Claptrap-Engineering/Mididuino/PCB Images/IMG_4418.JPG

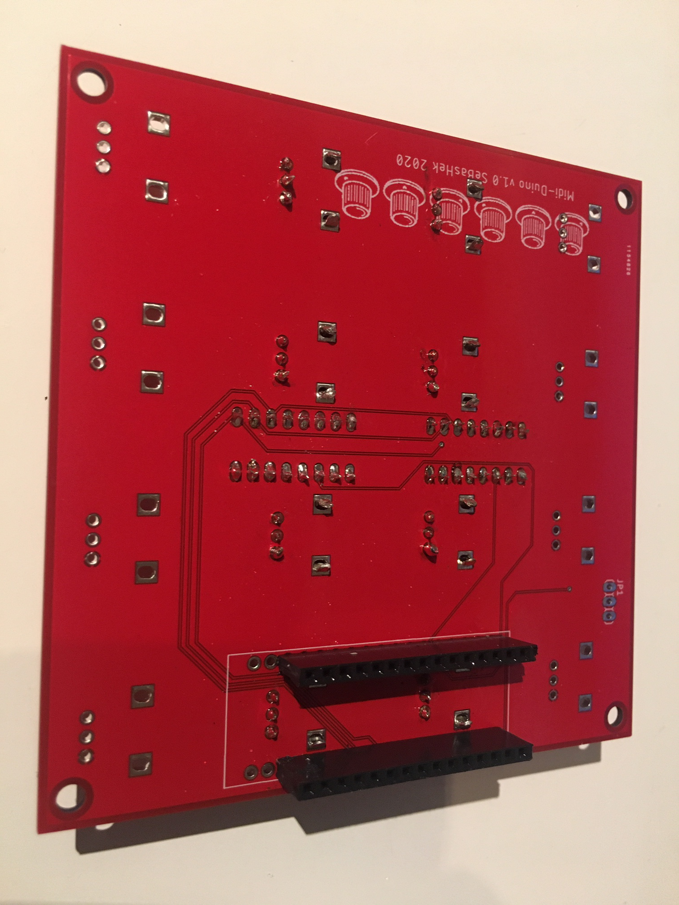
PCB Images/IMG_4418.JPG
