Claptrap-Engineering/Mididuino/PCB Images/IMG_4419.JPG

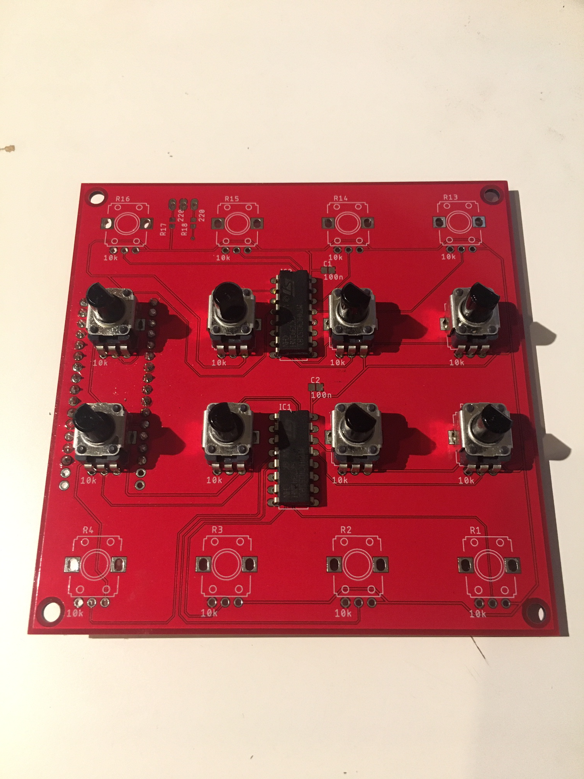
PCB Images/IMG_4419.JPG
